lukaslibar/Camera-Cooler/project-folder/firmware/C++/TEC_driver/pwm_fans.h

#pragma once

#include <cstdint>

using uint = unsigned int;

namespace pwmfan {
    // PWM FANS
    constexpr uint PIN1 = 2;
    constexpr uint PIN2 = 10;
    constexpr uint FEN_EN = 6;
    constexpr uint FREQ = 25000;

}
