lukaslibar/Camera-Cooler/project-folder/firmware/C++/FAN-control-example/fan_kontrol.cpp

#include "pico/stdlib.h"
#include "hardware/pwm.h"
#include "hardware/clocks.h"
#include "hardware/gpio.h"

constexpr uint PWM_PIN = 10;
constexpr uint FEN_EN = 6;
constexpr uint8_t DUTY_CYCLE = 30;
constexpr uint FREQ = 25000;

int main(){

    gpio_set_function(PWM_PIN, GPIO_FUNC_PWM);
    gpio_init(FEN_EN);

    uint slice_st = pwm_gpio_to_slice_num(PWM_PIN);
    uint kanal = pwm_gpio_to_channel(PWM_PIN);
    uint32_t ura = clock_get_hz(clk_sys);

    uint8_t DUTY_CYCLE_T = 100 - DUTY_CYCLE;
    uint wrap = ura / FREQ - 1;
    uint level = (DUTY_CYCLE_T * (wrap + 1)) / 100;

    pwm_set_clkdiv(slice_st, 1.0f); // brez deljenja ure
    pwm_set_wrap(slice_st, wrap);
    pwm_set_chan_level(slice_st, kanal, level);

    gpio_set_dir(FEN_EN, GPIO_IN); // GPIO mora biti nastavljen na vhod da lahko deluje v HiZ.

    pwm_set_enabled(slice_st, true);

    gpio_set_pulls(FEN_EN, false, false); // prižgan

    while (true)
    {
        tight_loop_contents();
    }
}
